maxned/TrailPi/Machine Learning/model_training/samples/online2.jpg

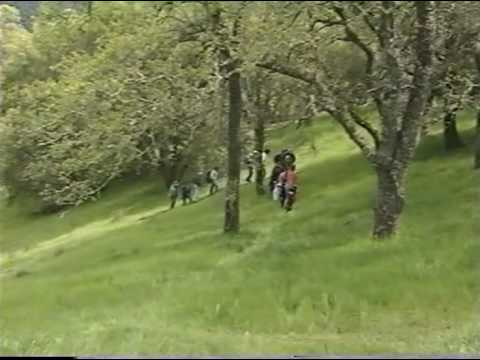
Machine Learning/model_training/samples/online2.jpg
