maxned/TrailPi/Machine Learning/model_training/samples/woodsonline.jpg

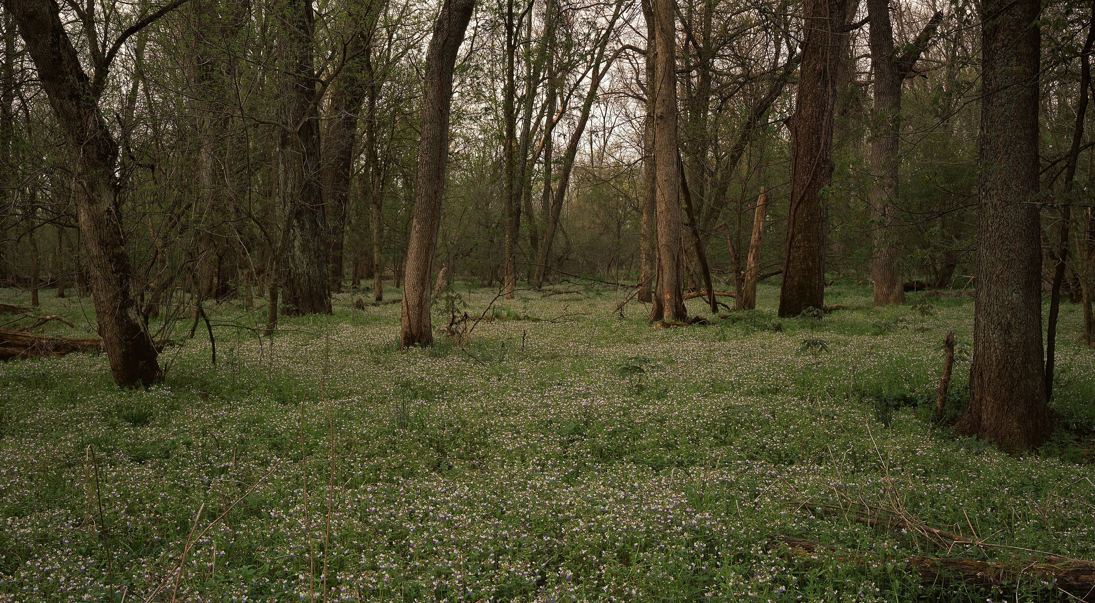
Machine Learning/model_training/samples/woodsonline.jpg
