maxned/TrailPi/Machine Learning/model_training/samples/deer.JPG

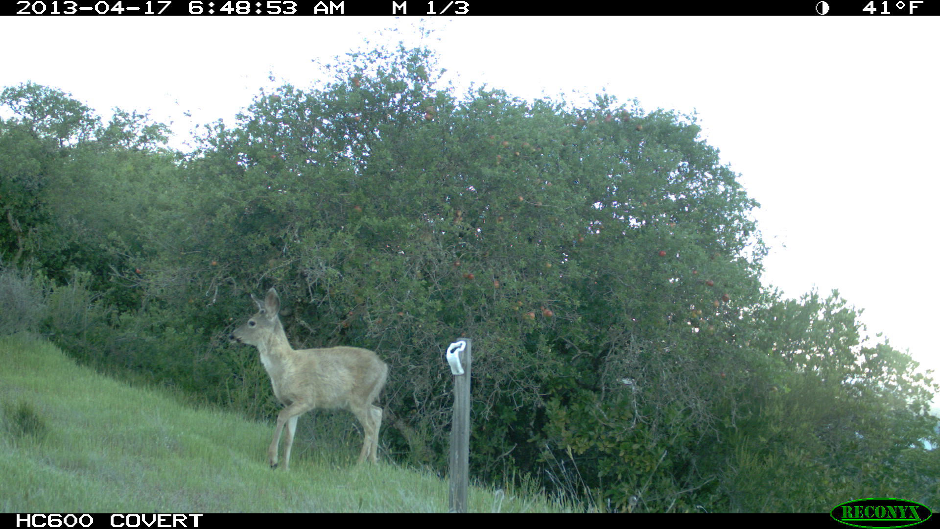
Machine Learning/model_training/samples/deer.JPG
