maxned/TrailPi/Machine Learning/model_training/samples/deeronline.jpg

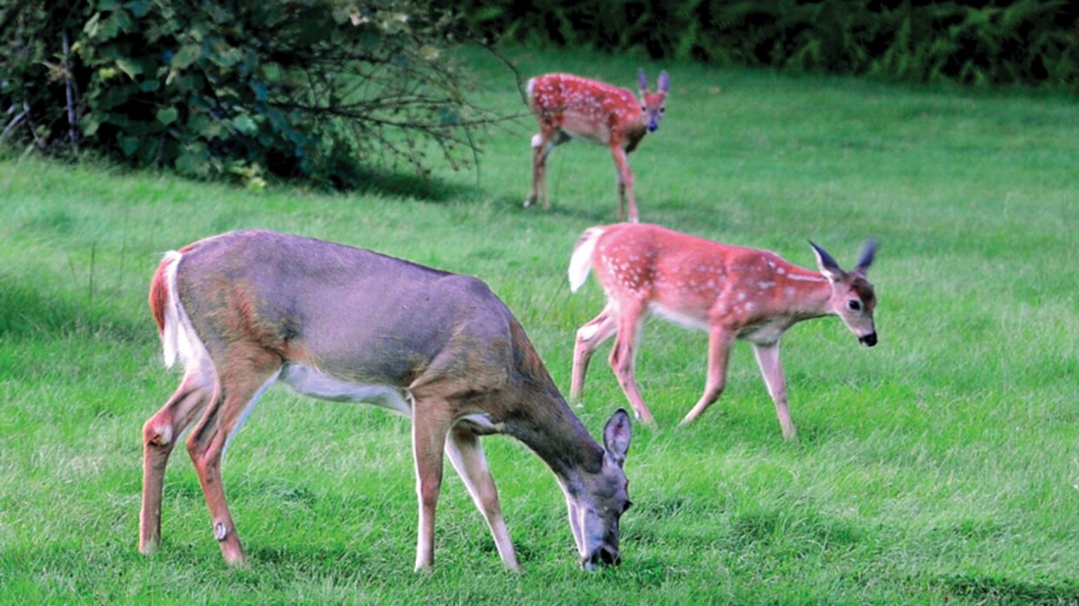
Machine Learning/model_training/samples/deeronline.jpg
