maxned/TrailPi/Machine Learning/model_training/samples/online1.jpg

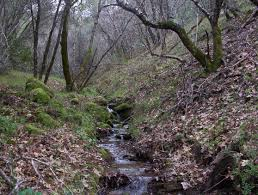
Machine Learning/model_training/samples/online1.jpg
