maxned/TrailPi/Machine Learning/model_training/samples/online3.jpg

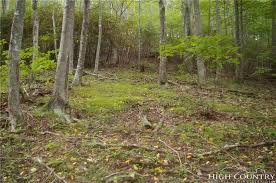
Machine Learning/model_training/samples/online3.jpg
