maxned/TrailPi/Machine Learning/model_training/samples/online4.jpg

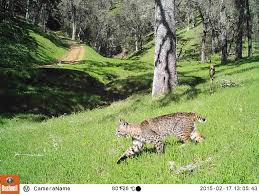
Machine Learning/model_training/samples/online4.jpg
